Scottapotamas/Quad1SLipoCharger/Regulator Notes/Curves.PNG

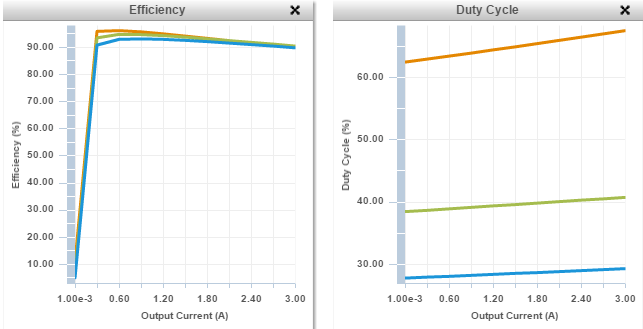
Regulator Notes/Curves.PNG
