Scottapotamas/Quad1SLipoCharger/Regulator Notes/Layout.PNG

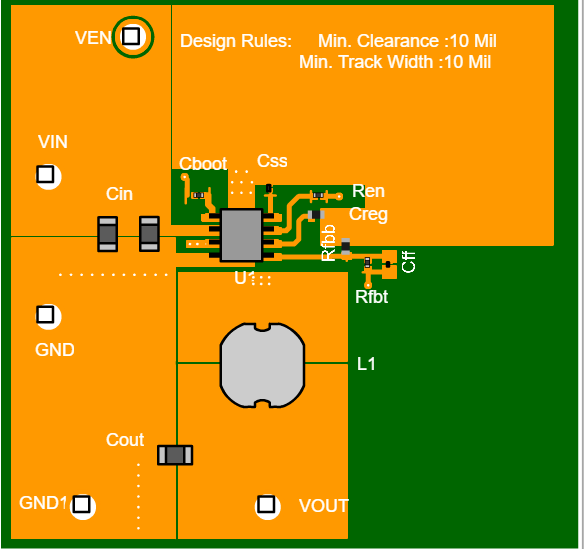
Regulator Notes/Layout.PNG
